MiataMike/Hydratelyn/Divider.asc

R1: res; {R}
R2: res; 10
R3: res; {R}
R4: res; 1000
R5: res; {R}
R6: res; 100000
R7: res; {R}
R8: res; 1000000
V1: voltage; 1
Named nets: 0
.step dec param R 1 1000000 10
.op
